iwmsl/klp-lame-keycaps/OpenSCAD/STL/Choc Stem + MX Tight Size/Choc_Stem_MX_Tight_Size_Angular_1.5U_Normal.stl

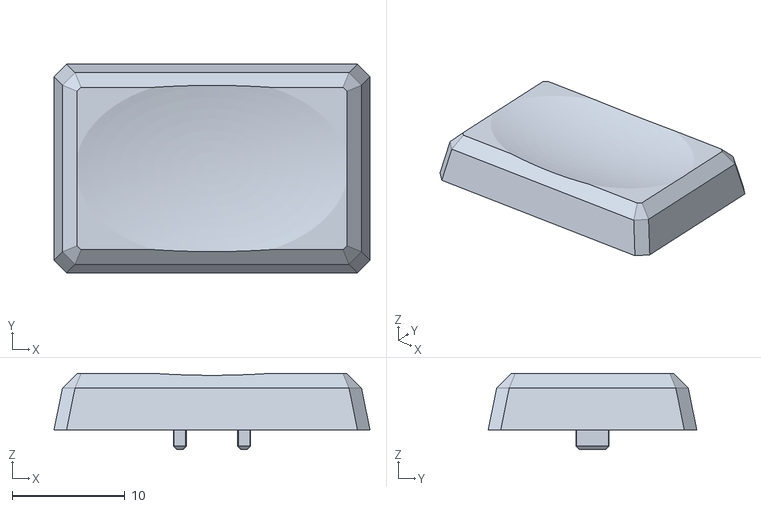
[picture p21: CAD file, 2026-08-04]
OpenSCAD/STL/Choc Stem + MX Tight Size/Choc_Stem_MX_Tight_Size_Angular_1.5U_Normal.stl
28.0 x 18.5 x 6.76
