iwmsl/klp-lame-keycaps/OpenSCAD/STL/MX Stem + Choc Size/MX_Stem_Choc_Size_Angular_Normal_Tilted.stl

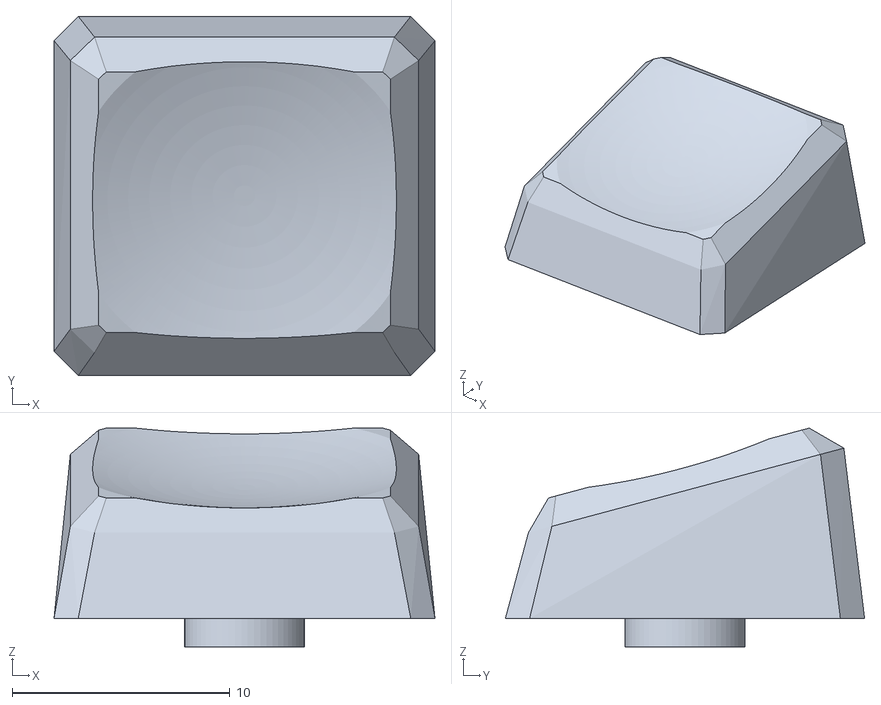
[picture p22: CAD file, 2026-08-04]
OpenSCAD/STL/MX Stem + Choc Size/MX_Stem_Choc_Size_Angular_Normal_Tilted.stl
17.5 x 16.5 x 10.0
