iwmsl/klp-lame-keycaps/OpenSCAD/STL/MX Stem + MX Size/MX_Stem_MX_Size_Angular_Normal_Tilted.stl

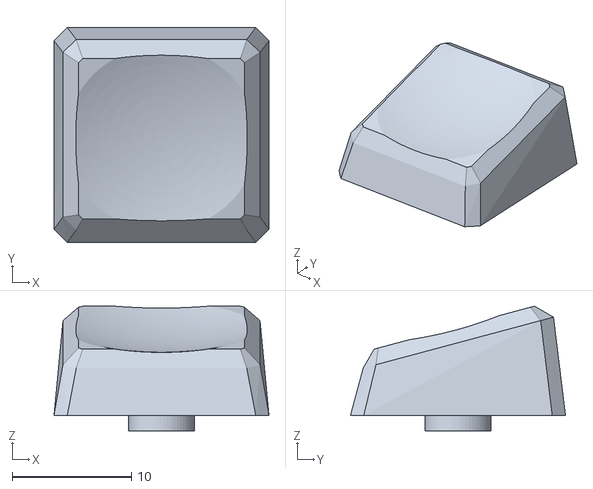
[picture p23: CAD file, 2026-08-04]
OpenSCAD/STL/MX Stem + MX Size/MX_Stem_MX_Size_Angular_Normal_Tilted.stl
18.0 x 18.0 x 10.4
