iwmsl/klp-lame-keycaps/OpenSCAD/STL/Choc Stem + Choc Size/Choc_Stem_Choc_Size_Angular_Normal_Homing.stl

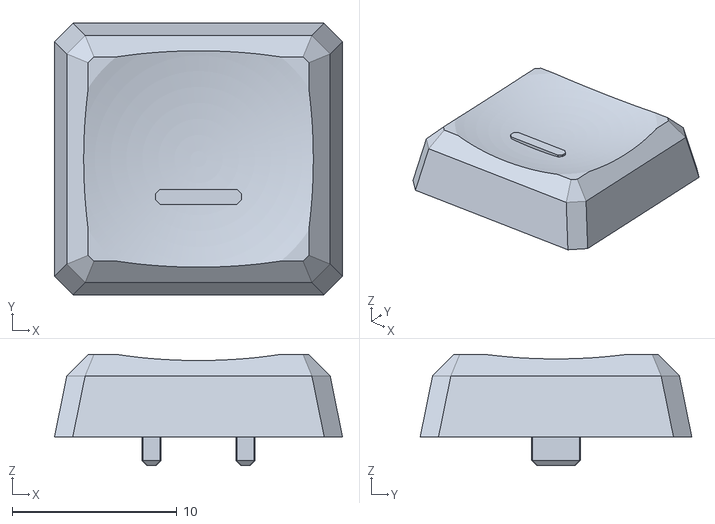
[picture p24: CAD file, 2026-08-04]
OpenSCAD/STL/Choc Stem + Choc Size/Choc_Stem_Choc_Size_Angular_Normal_Homing.stl
17.5 x 16.5 x 6.76
