iwmsl/klp-lame-keycaps/OpenSCAD/STL/MX Stem + MX Size/MX_Stem_MX_Size_Angular_1.5U_Normal.stl

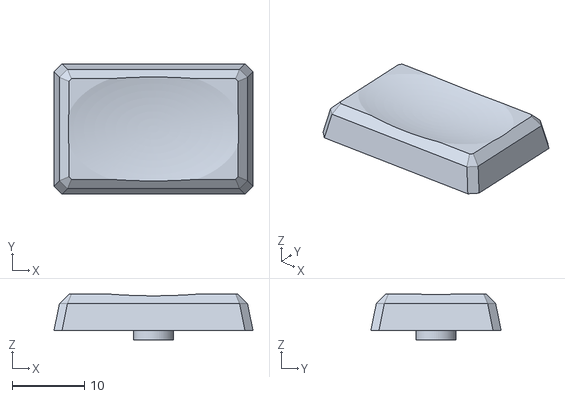
[picture p25: CAD file, 2026-08-04]
OpenSCAD/STL/MX Stem + MX Size/MX_Stem_MX_Size_Angular_1.5U_Normal.stl
27.5 x 18.0 x 6.31
